Danjovic/Phoenician_Clock/doc/IMG_20230629_204120289.jpg

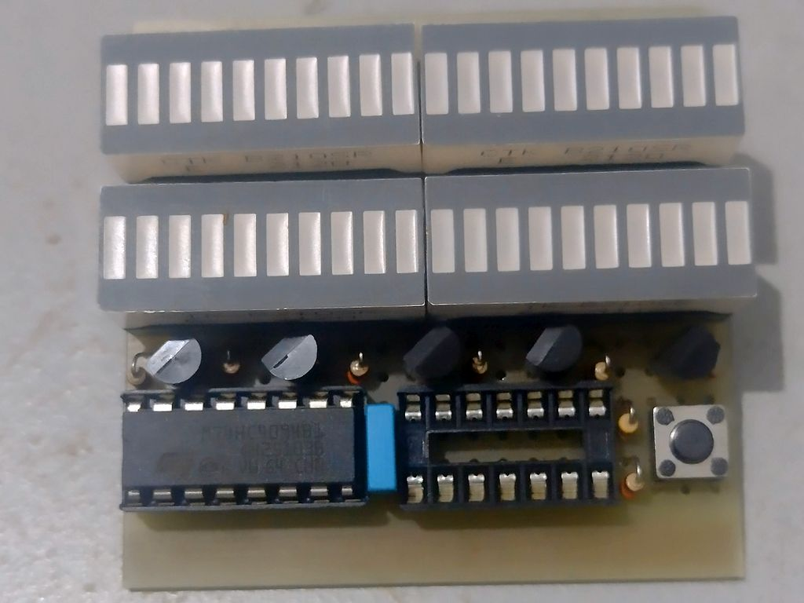
doc/IMG_20230629_204120289.jpg
